BrianLeishman/blip/enclosure/stl/tapered-face-fit-m25.stl

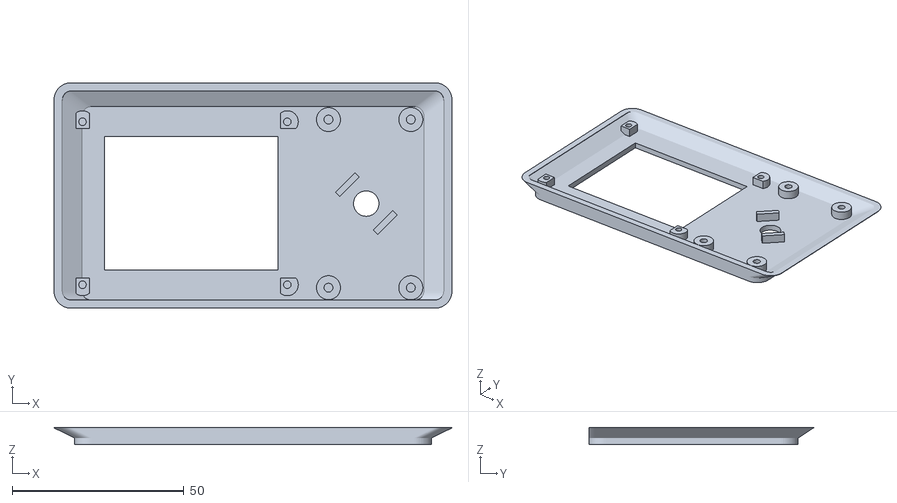
[picture p16: CAD file, 2026-09-24]
enclosure/stl/tapered-face-fit-m25.stl
116.0 x 65.7 x 5.00
