BrianLeishman/blip/enclosure/stl/v2-print-layout.stl

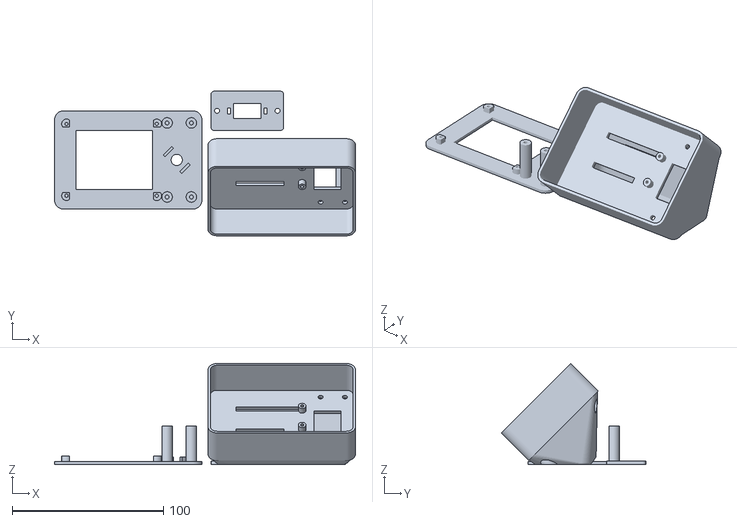
[picture p17: CAD file, 2026-09-24]
enclosure/stl/v2-print-layout.stl
199.1 x 95.7 x 66.8
