BrianLeishman/blip/enclosure/stl/front.stl

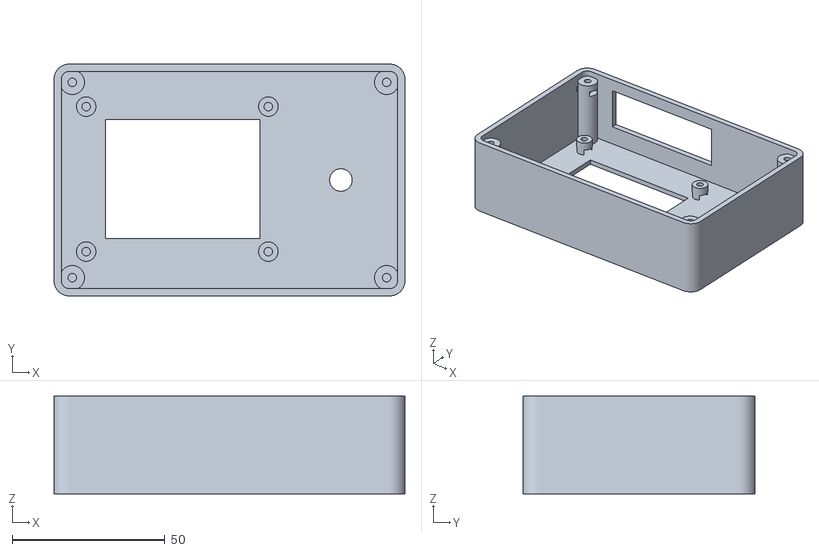
[picture p18: CAD file, 2026-09-21]
enclosure/stl/front.stl
115.0 x 76.0 x 32.0
