BrianLeishman/blip/enclosure/v2/dimensions.scad

// XY facts extracted from Adafruit Eagle CAD. See vendor-dimensions.json.
// Board thickness and component heights are deliberately NOT inferred.
screen_xy = [52.578, 64.77];
screen_holes = [[2.54, 2.54, 2.5], [50.038, 2.54, 2.5], [2.54, 62.23, 2.5], [50.038, 62.23, 2.5]];
feather_xy = [50.8, 22.86];
feather_holes = [[2.54, 20.32, 2.5], [2.54, 2.54, 2.5]];
encoder_xy = [25.4, 25.4];
encoder_holes = [[2.54, 22.86, 2.5], [22.86, 22.86, 2.5], [2.54, 2.54, 2.5], [22.86, 2.54, 2.5]];
